jsenzel1/supra/supra firmware source complete/bitmaps.c

const unsigned char rhbmp []  = {
0x00, 0x00, 0xc0, 0x00, 0x00, 0x00, 0x00, 0x00, 0x00, 0x00, 0x00, 0x00, 0x00, 0x00, 0x00, 0x18, 
	0x10, 0x02, 0x00, 0x00, 0x00, 0x00, 0x24, 0x10, 0x02, 0x00, 0x00, 0x00, 0x00, 0x44, 0x10, 0x02, 
	0x60, 0x00, 0x00, 0x00, 0x40, 0x10, 0x02, 0x80, 0x00, 0x00, 0x00, 0x42, 0x10, 0x02, 0x80, 0x00, 
	0x00, 0x00, 0x44, 0x10, 0x02, 0x84, 0x00, 0x00, 0x00, 0x44, 0x10, 0x02, 0x84, 0x00, 0x00, 0x00, 
	0x44, 0x10, 0x04, 0x84, 0x00, 0x00, 0x00, 0x84, 0x10, 0x04, 0x42, 0x00, 0x00, 0x00, 0x84, 0x10, 
	0x04, 0x42, 0x00, 0x00, 0x04, 0x84, 0x10, 0x04, 0x42, 0x00, 0x00, 0x08, 0x08, 0x11, 0x04, 0x40, 
	0x00, 0x00, 0x11, 0x08, 0x11, 0x04, 0x21, 0x00, 0x00, 0x11, 0x08, 0x11, 0x84, 0x20, 0x00, 0x00, 
	0x21, 0x08, 0x12, 0x84, 0x20, 0x00, 0x00, 0x22, 0x08, 0x12, 0x84, 0x20, 0x00, 0x00, 0x42, 0x08, 
	0x12, 0x44, 0x10, 0x00, 0x00, 0x44, 0x08, 0x12, 0x44, 0x10, 0x00, 0x00, 0x84, 0x10, 0x12, 0x24, 
	0x08, 0x00, 0x00, 0x08, 0x11, 0x14, 0x24, 0x08, 0x00, 0x00, 0x08, 0x11, 0x14, 0x18, 0x04, 0x00, 
	0x00, 0x10, 0x22, 0x08, 0x00, 0x04, 0x00, 0x00, 0x10, 0x24, 0x00, 0x00, 0x04, 0x00, 0x00, 0x20, 
	0x18, 0x00, 0x00, 0x04, 0x00, 0x00, 0x40, 0x00, 0x00, 0x00, 0x04, 0x00, 0x00, 0x80, 0x00, 0x00, 
	0x00, 0x04, 0x80, 0x0f, 0x80, 0x00, 0x00, 0x00, 0x02, 0x70, 0x10, 0x80, 0x00, 0x00, 0x00, 0x02, 
	0x00, 0x10, 0x80, 0x00, 0x00, 0x00, 0x02, 0x04, 0x0c, 0x80, 0x00, 0x00, 0x00, 0x01, 0x02, 0x02, 
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
};

// Array of all bitmaps for convenience. (Total bytes used to store images in PROGMEM = 16640)
const unsigned char* clkArray[16] = {
	cclk1,
	cclk2,
	cclk3,
	cclk4,
	cclk5,
	cclk6,
	cclk7,
	cclk8,
	cclk9,
	cclk10,
	cclk11,
	cclk12,
	cclk13,
	cclk14,
	cclk15,
	cclk16
};
